jmalenko/us8ek/70-photo/PXL_20260111_123954329.jpg

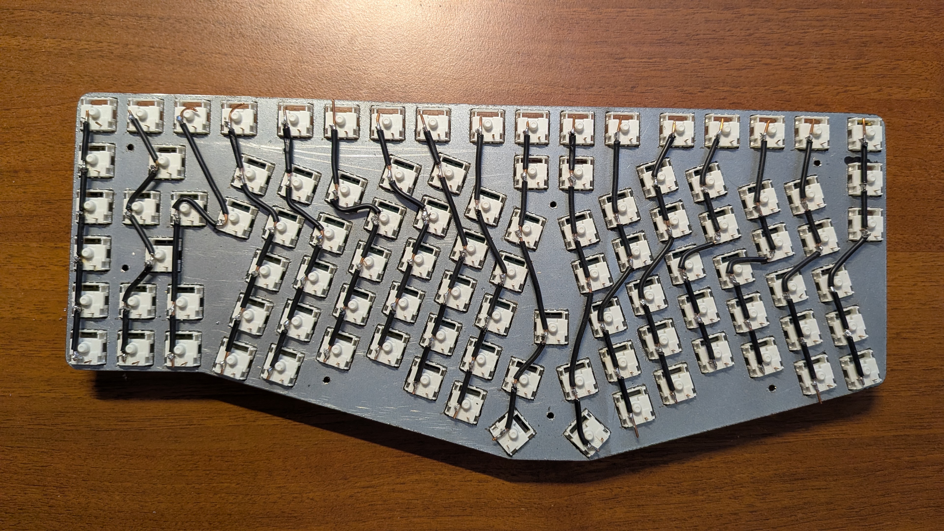
70-photo/PXL_20260111_123954329.jpg
