jmalenko/us8ek/70-photo/PXL_20260111_124021792.jpg

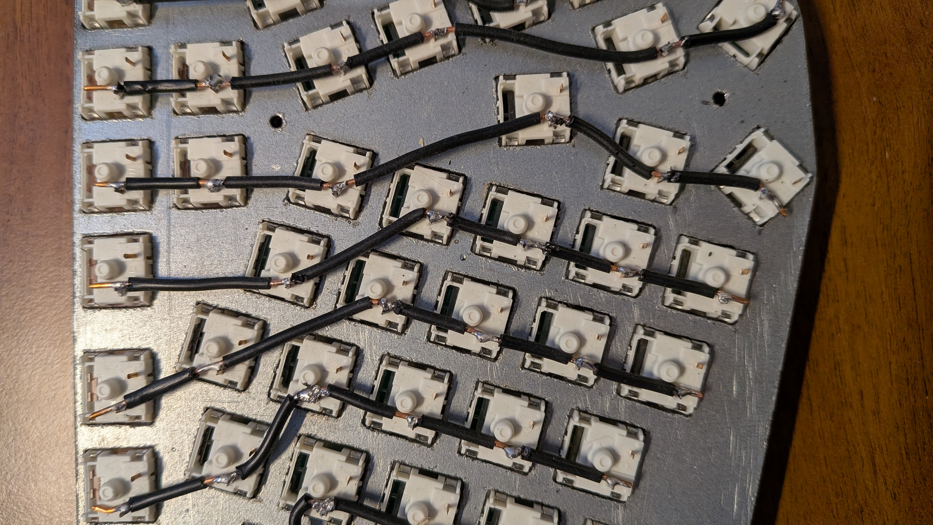
70-photo/PXL_20260111_124021792.jpg
