jmalenko/us8ek/70-photo/PXL_20260111_124031292.jpg

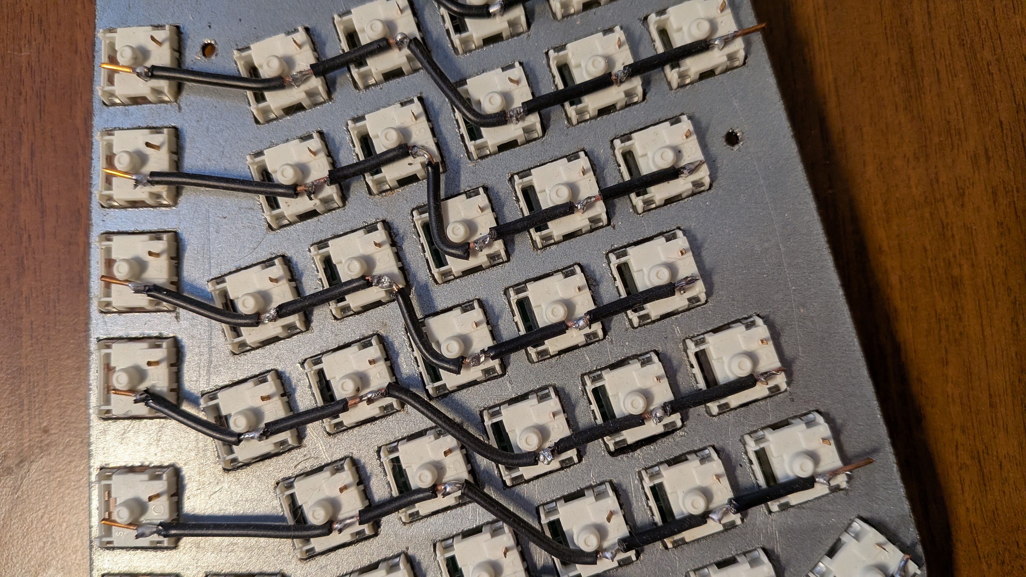
70-photo/PXL_20260111_124031292.jpg
