jmalenko/us8ek/70-photo/PXL_20260111_124134626.jpg

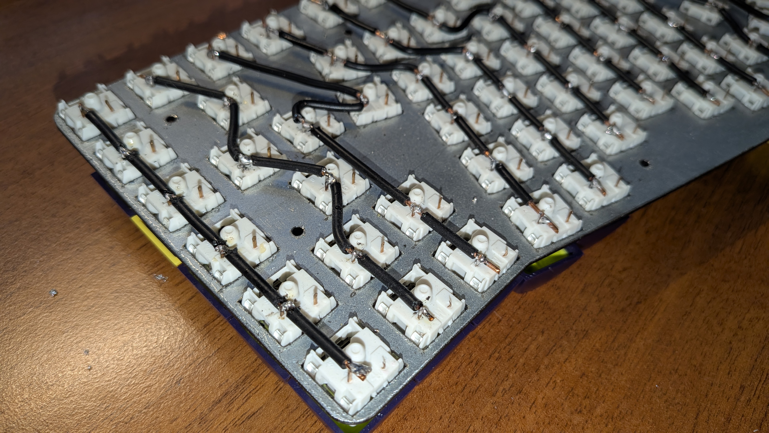
70-photo/PXL_20260111_124134626.jpg
