jmalenko/us8ek/70-photo/PXL_20260111_124154416.jpg

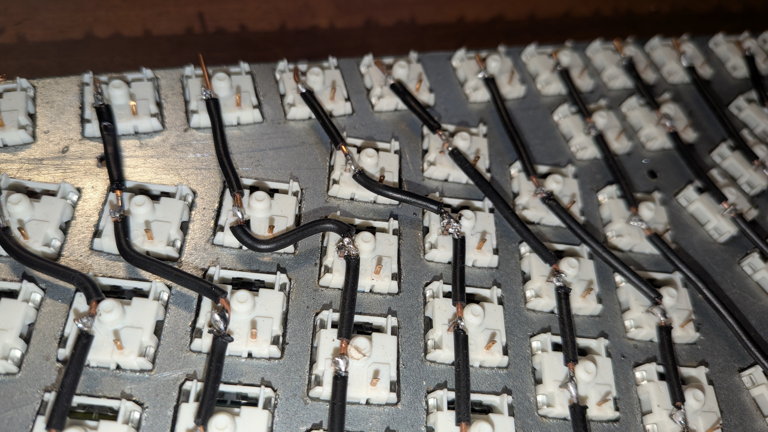
70-photo/PXL_20260111_124154416.jpg
