jmalenko/us8ek/70-photo/PXL_20260111_124345939.jpg

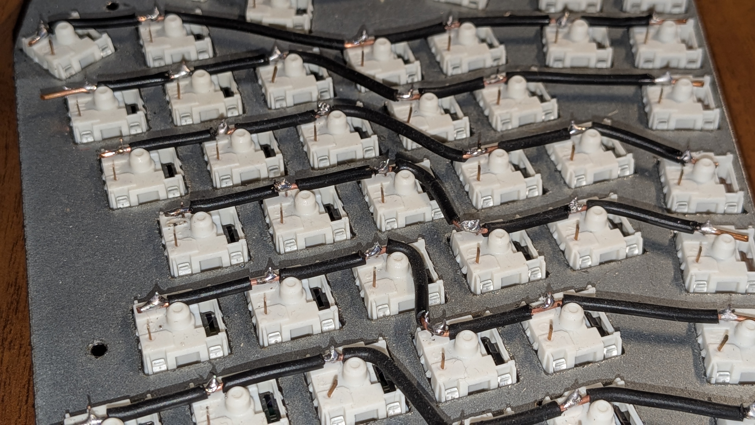
70-photo/PXL_20260111_124345939.jpg
