jmalenko/us8ek/70-photo/PXL_20260111_124404799.jpg

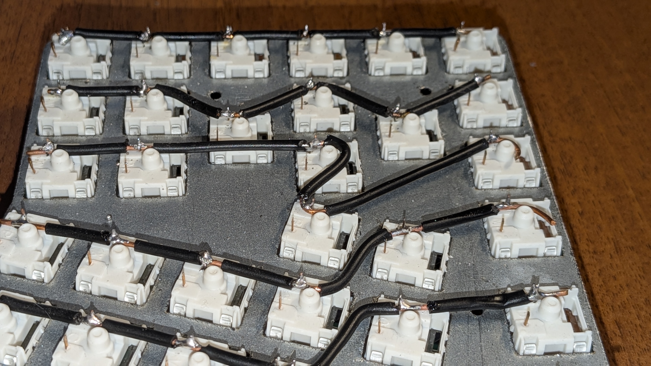
70-photo/PXL_20260111_124404799.jpg
