jmalenko/us8ek/70-photo/PXL_20260111_125549757.jpg

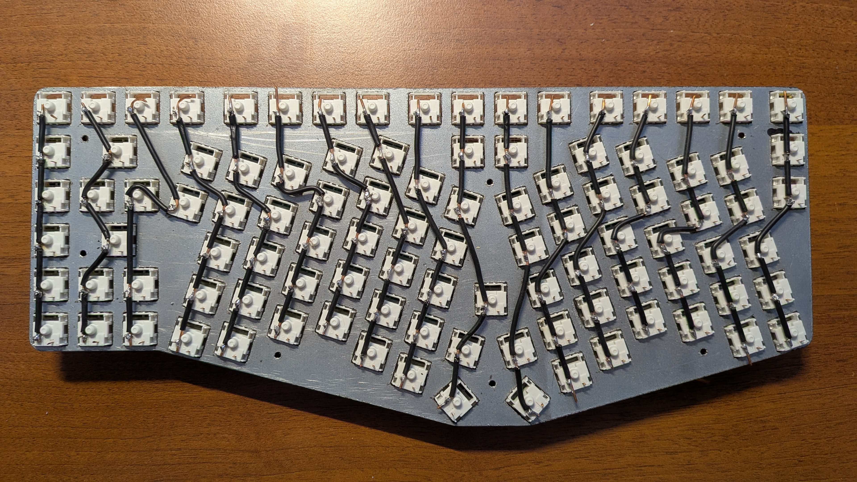
70-photo/PXL_20260111_125549757.jpg
