jmalenko/us8ek/70-photo/PXL_20260111_170305145.jpg

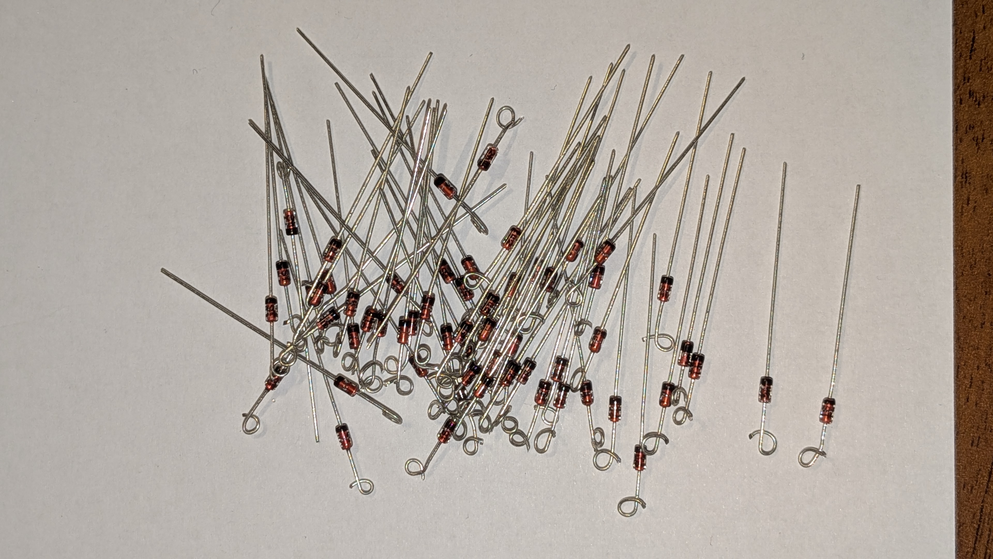
70-photo/PXL_20260111_170305145.jpg
