jmalenko/us8ek/70-photo/PXL_20260111_181909219.jpg

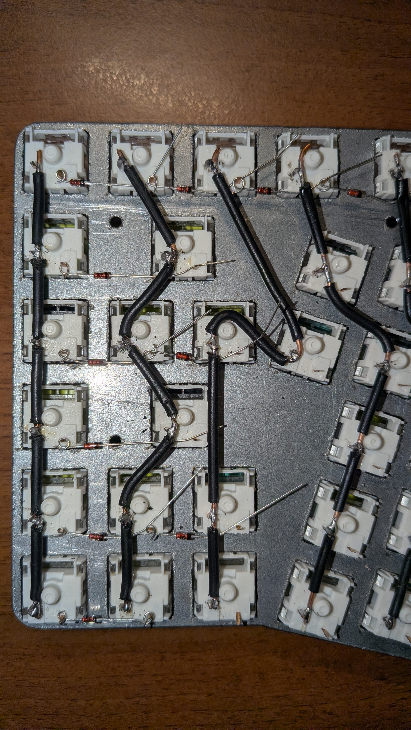
70-photo/PXL_20260111_181909219.jpg
