jmalenko/us8ek/70-photo/PXL_20260113_114841229.jpg

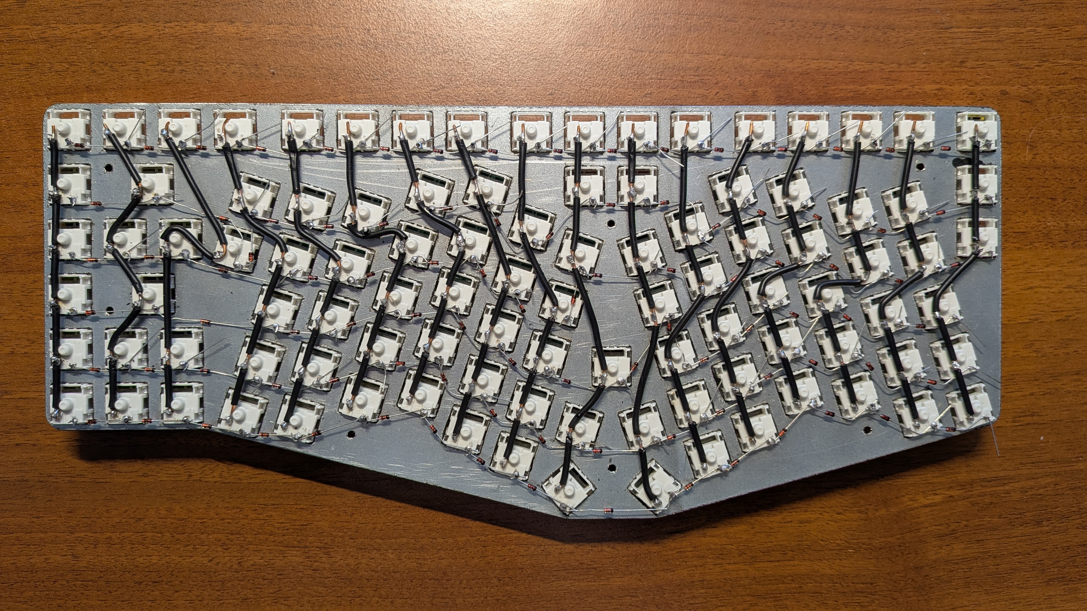
70-photo/PXL_20260113_114841229.jpg
