jmalenko/us8ek/70-photo/PXL_20260113_114855864.jpg

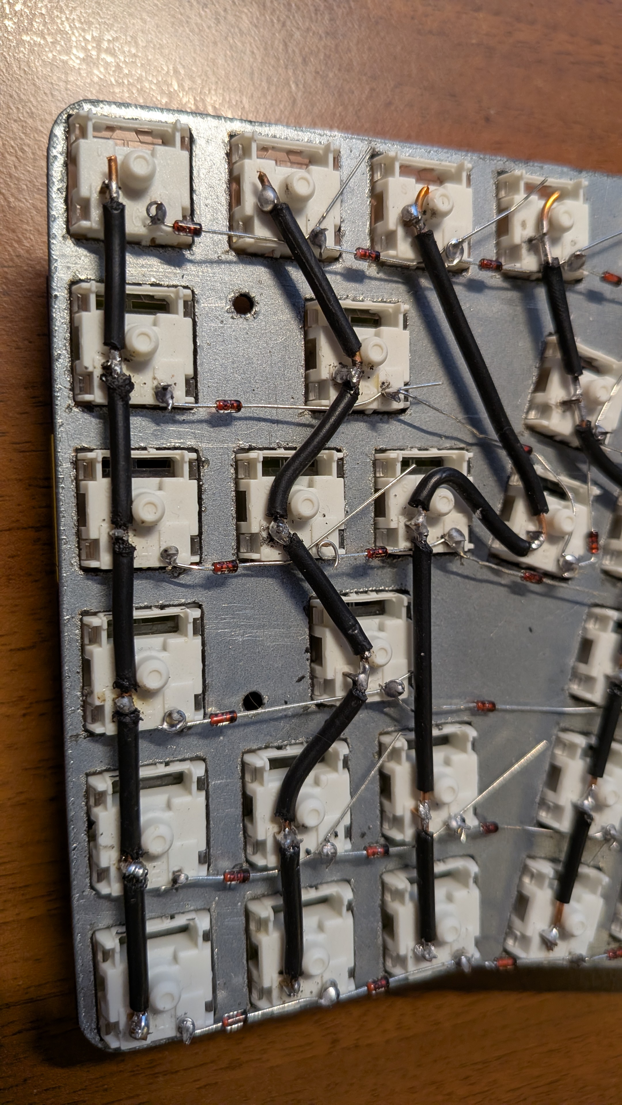
70-photo/PXL_20260113_114855864.jpg
