jmalenko/us8ek/70-photo/PXL_20260113_114857588.jpg

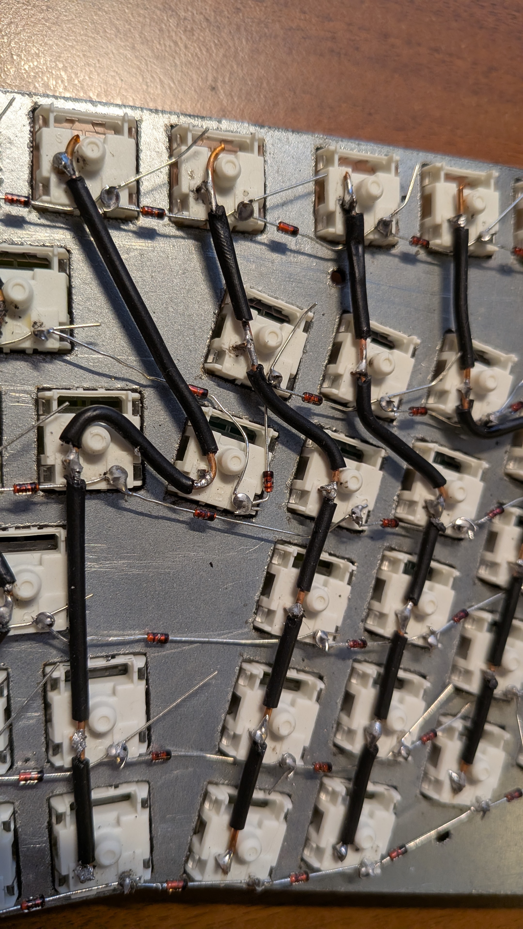
70-photo/PXL_20260113_114857588.jpg
