jmalenko/us8ek/70-photo/PXL_20260113_114900836.jpg

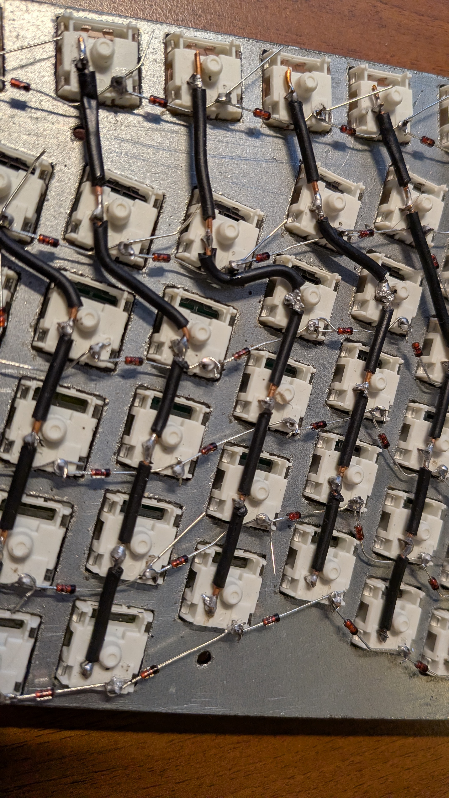
70-photo/PXL_20260113_114900836.jpg
