jmalenko/us8ek/70-photo/PXL_20260113_114911246.jpg

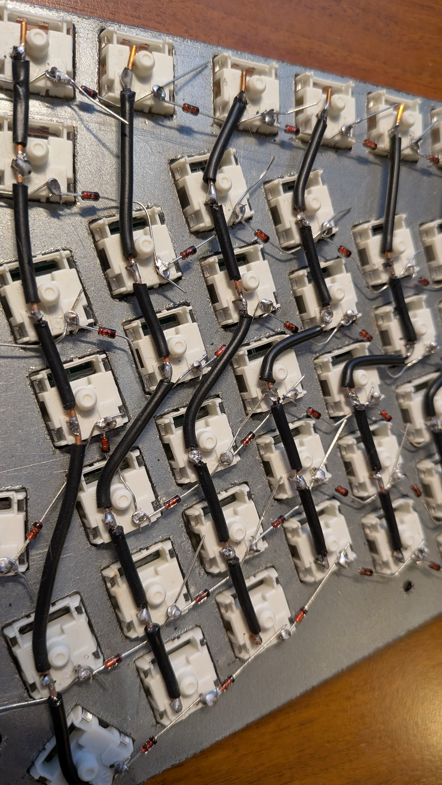
70-photo/PXL_20260113_114911246.jpg
