jmalenko/us8ek/70-photo/PXL_20260113_114915414.MACRO_FOCUS.jpg

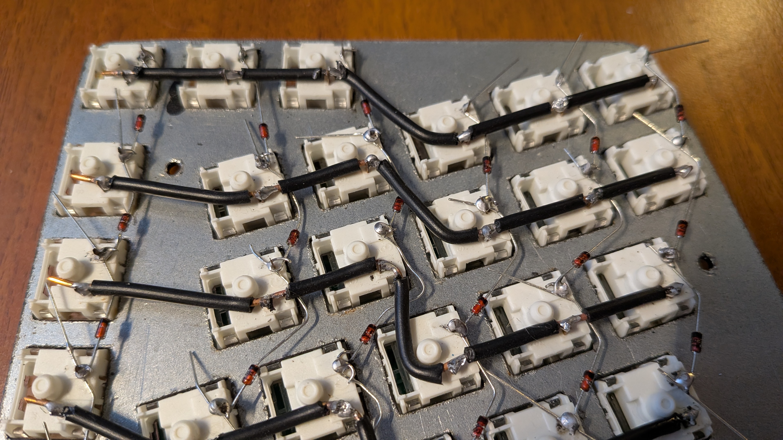
70-photo/PXL_20260113_114915414.MACRO_FOCUS.jpg
