jmalenko/us8ek/70-photo/PXL_20260113_120844157.jpg

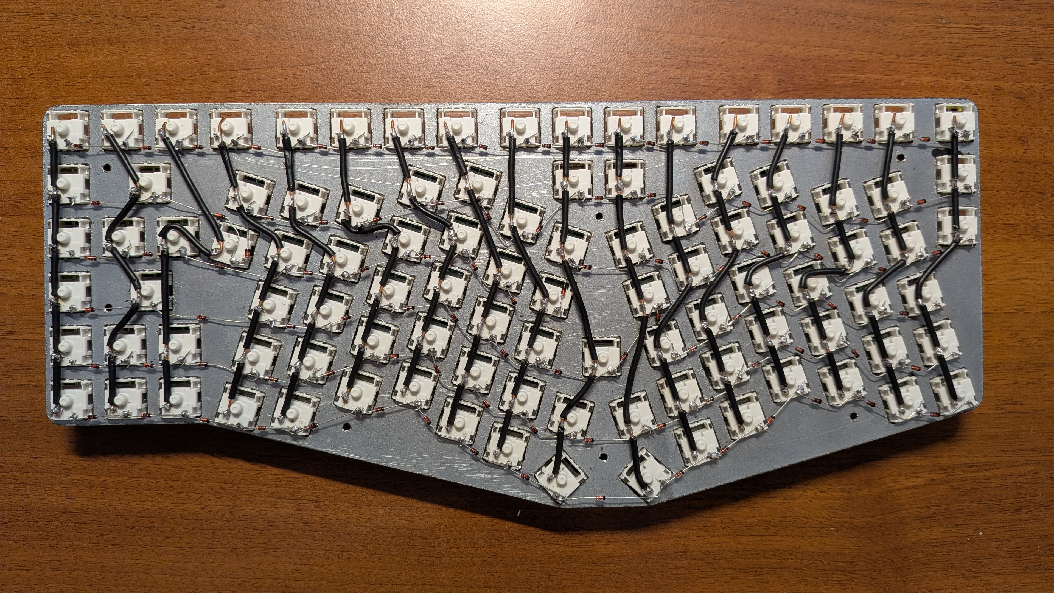
70-photo/PXL_20260113_120844157.jpg
