jmalenko/us8ek/70-photo/PXL_20260113_120919098.jpg

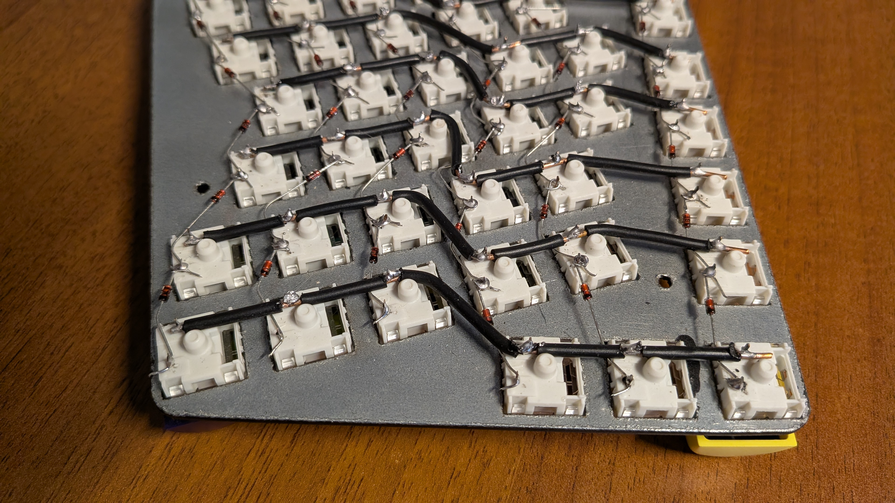
70-photo/PXL_20260113_120919098.jpg
