jmalenko/us8ek/70-photo/PXL_20260113_120921176.jpg

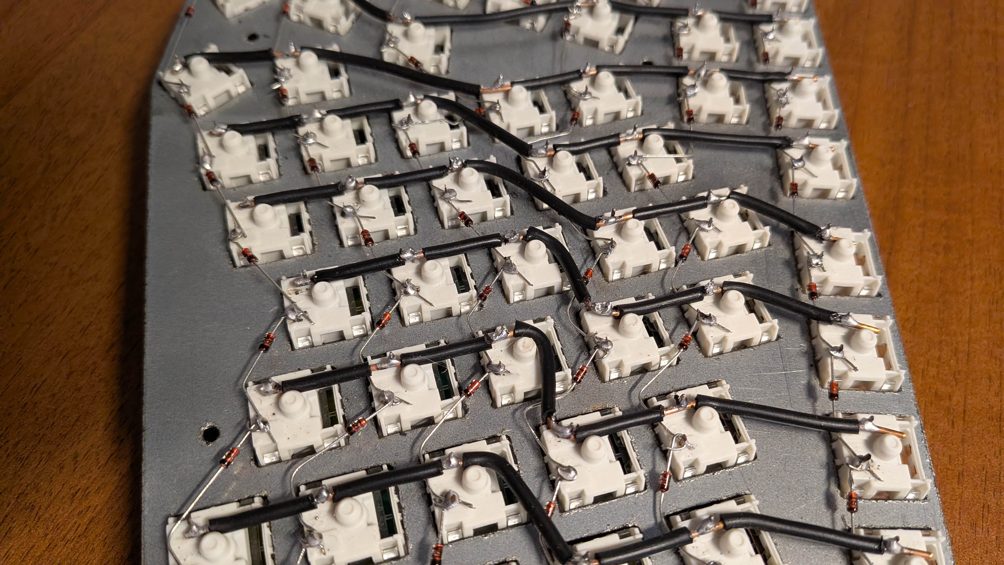
70-photo/PXL_20260113_120921176.jpg
