jmalenko/us8ek/70-photo/PXL_20260113_120925056.jpg

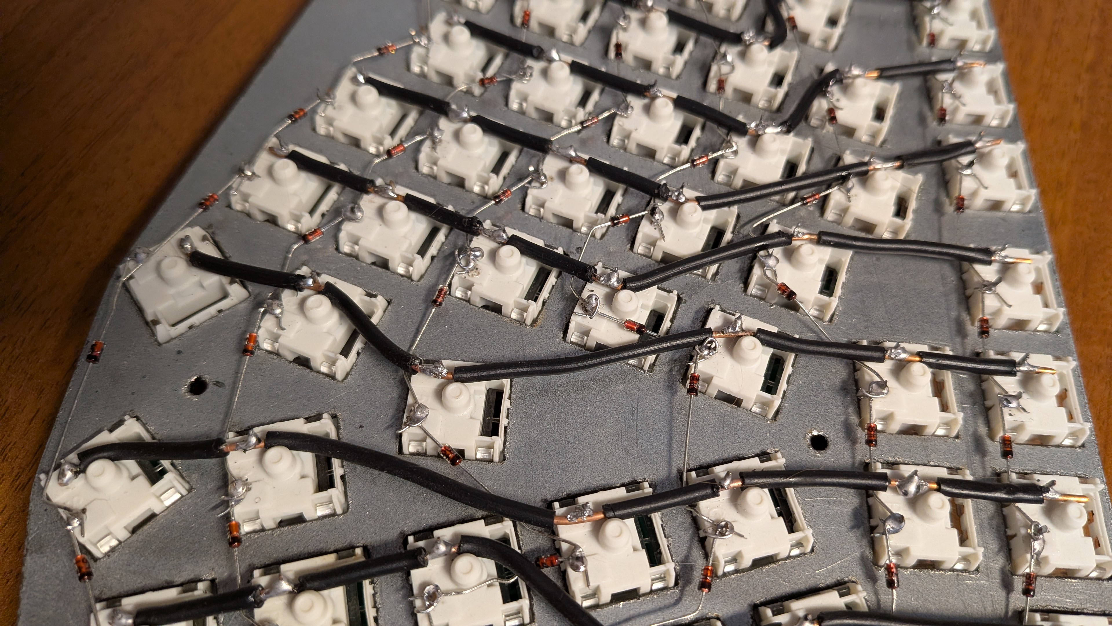
70-photo/PXL_20260113_120925056.jpg
