jmalenko/us8ek/70-photo/PXL_20260113_120930169.jpg

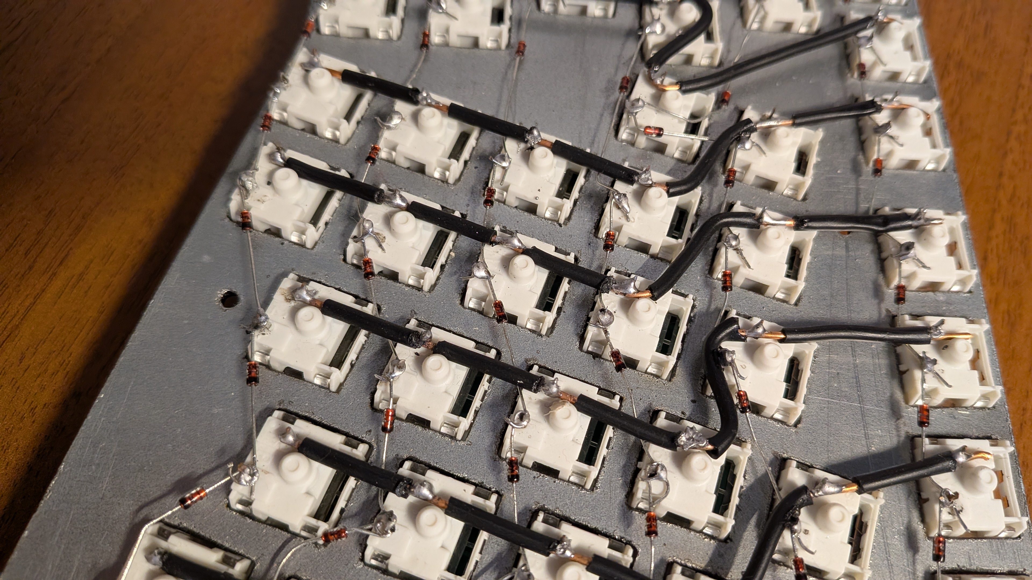
70-photo/PXL_20260113_120930169.jpg
