jmalenko/us8ek/70-photo/PXL_20260113_120933175.jpg

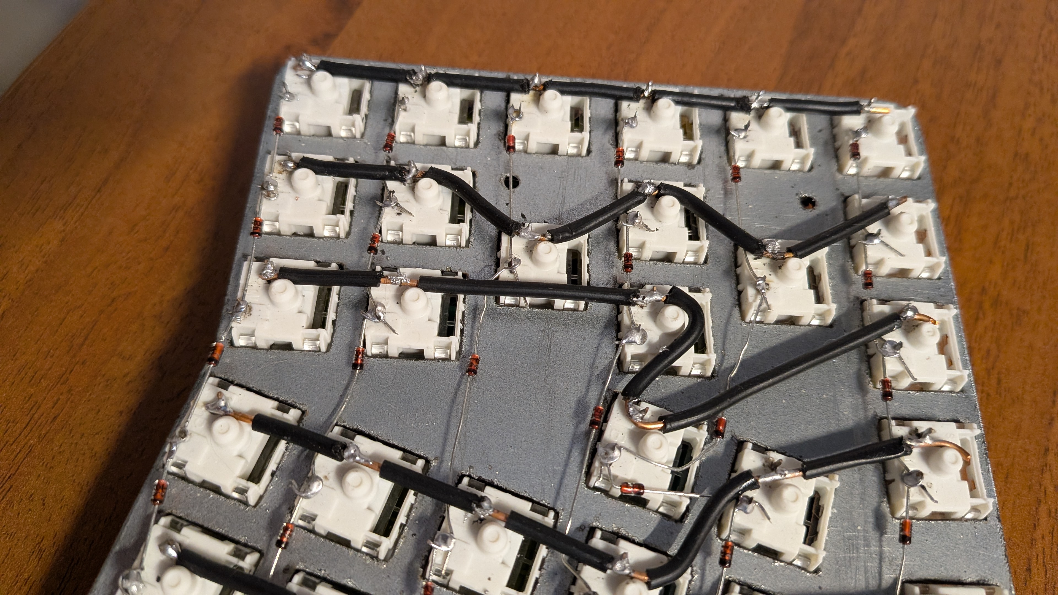
70-photo/PXL_20260113_120933175.jpg
