jmalenko/us8ek/70-photo/PXL_20260113_120949158.jpg

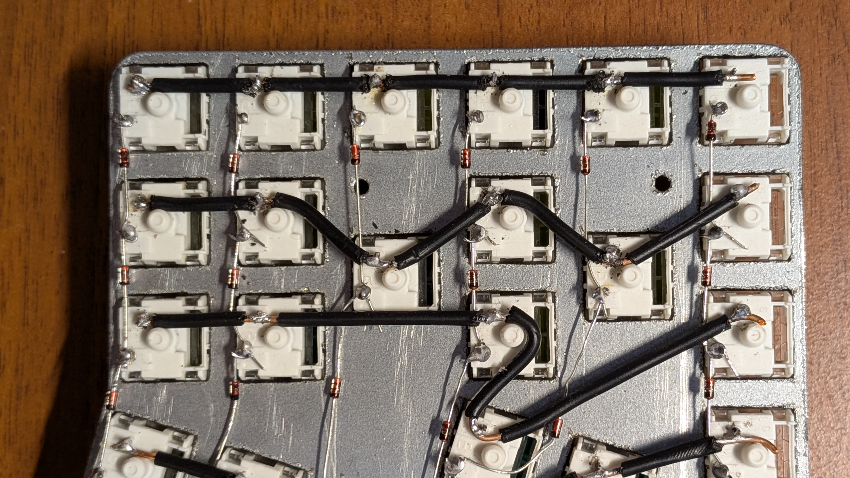
70-photo/PXL_20260113_120949158.jpg
