jmalenko/us8ek/70-photo/PXL_20260113_120952211.jpg

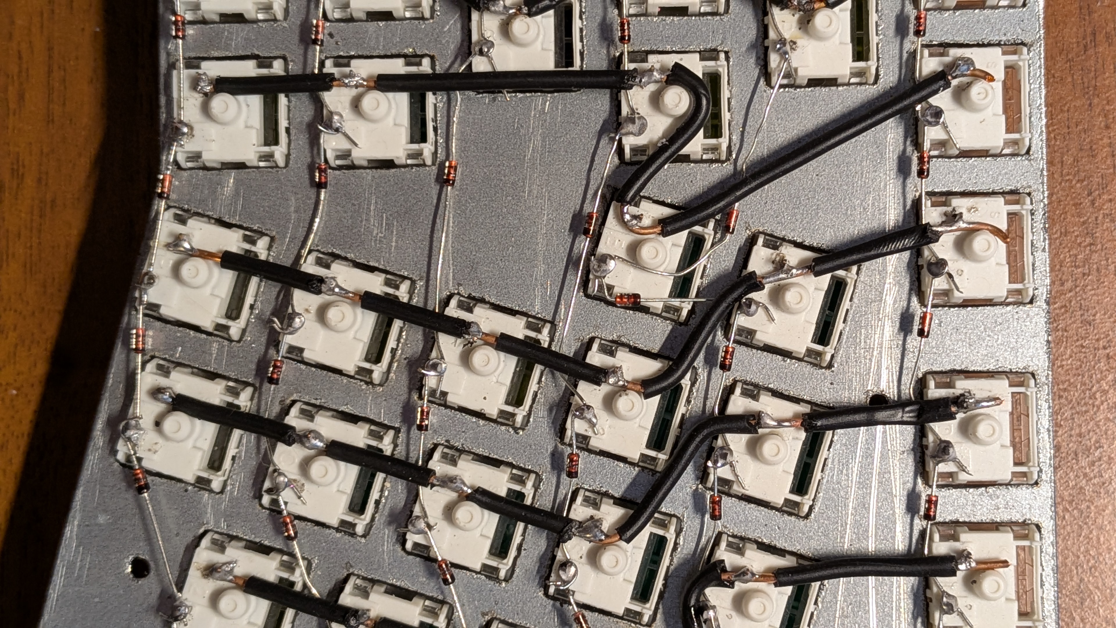
70-photo/PXL_20260113_120952211.jpg
