jmalenko/us8ek/70-photo/PXL_20260113_120954827.jpg

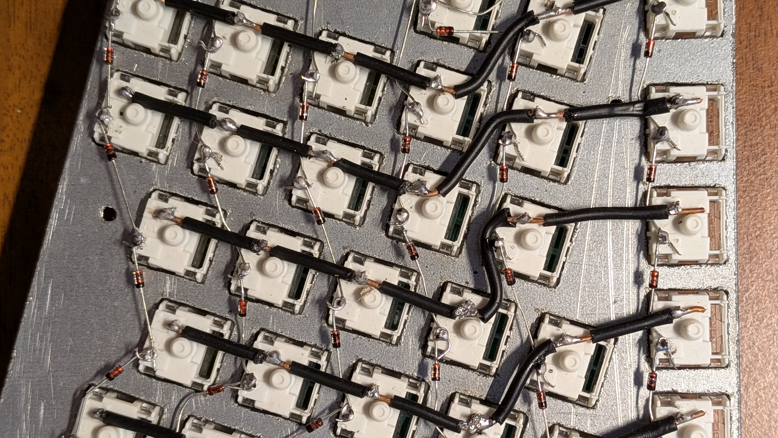
70-photo/PXL_20260113_120954827.jpg
