jmalenko/us8ek/70-photo/PXL_20260113_120957864.jpg

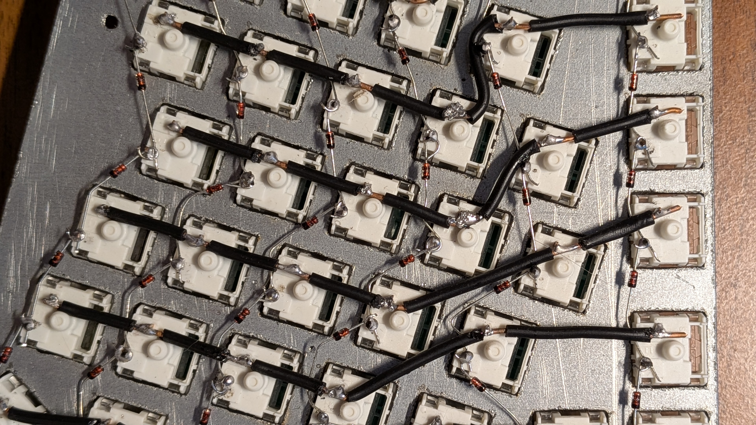
70-photo/PXL_20260113_120957864.jpg
