jmalenko/us8ek/70-photo/PXL_20260113_121008801.jpg

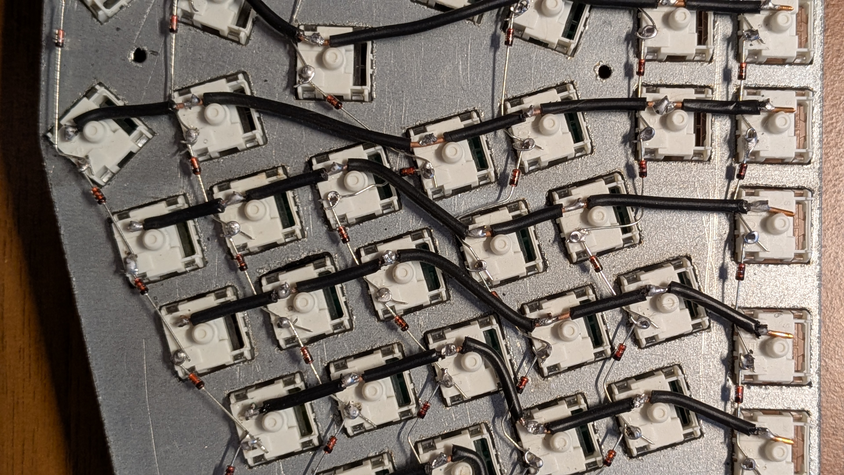
70-photo/PXL_20260113_121008801.jpg
