jmalenko/us8ek/70-photo/PXL_20260113_121011084.jpg

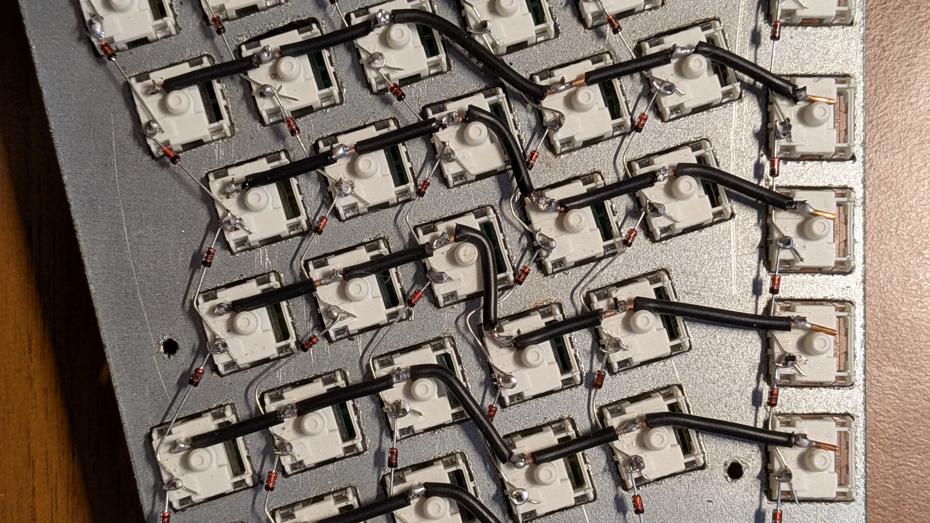
70-photo/PXL_20260113_121011084.jpg
