jmalenko/us8ek/70-photo/PXL_20260113_160840646.jpg

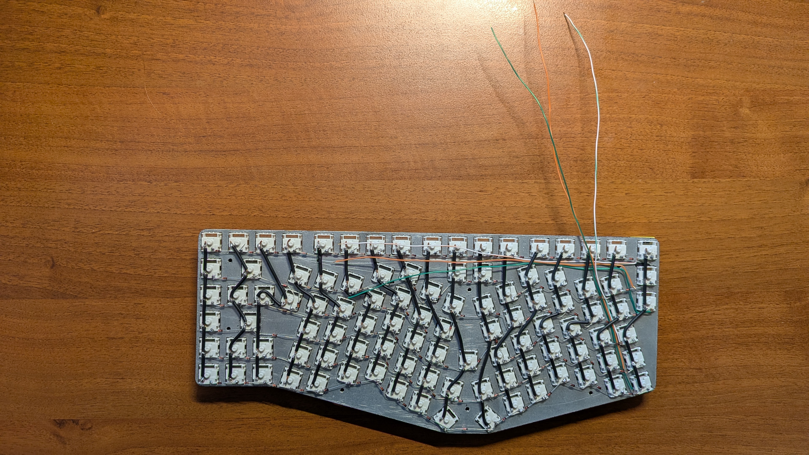
70-photo/PXL_20260113_160840646.jpg
