jmalenko/us8ek/70-photo/PXL_20260113_171134061.jpg

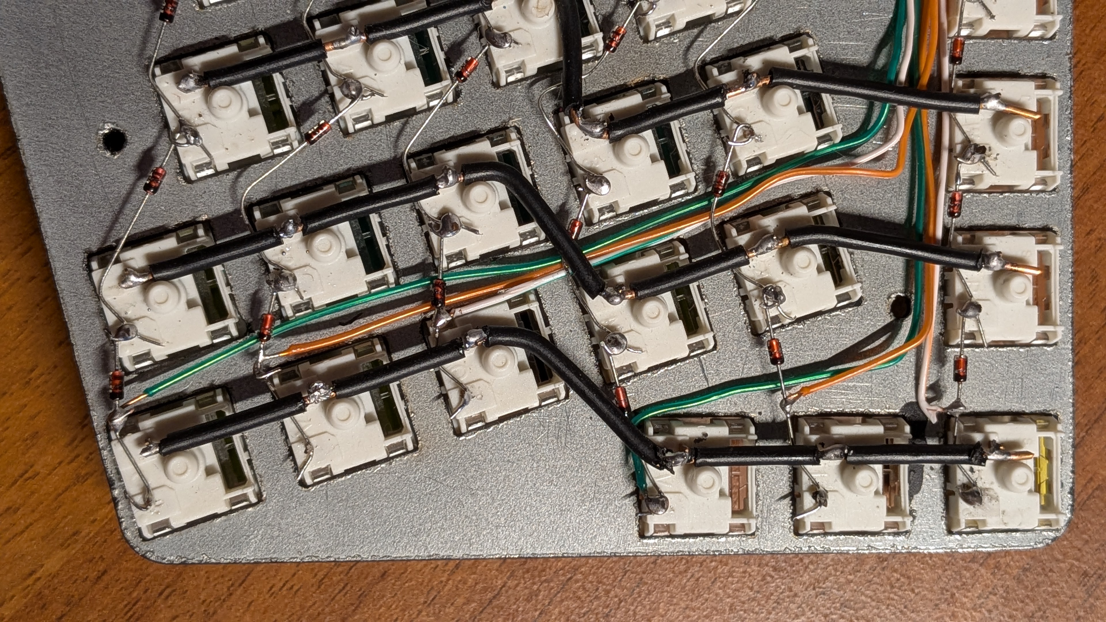
70-photo/PXL_20260113_171134061.jpg
