jmalenko/us8ek/70-photo/PXL_20260113_171150978.jpg

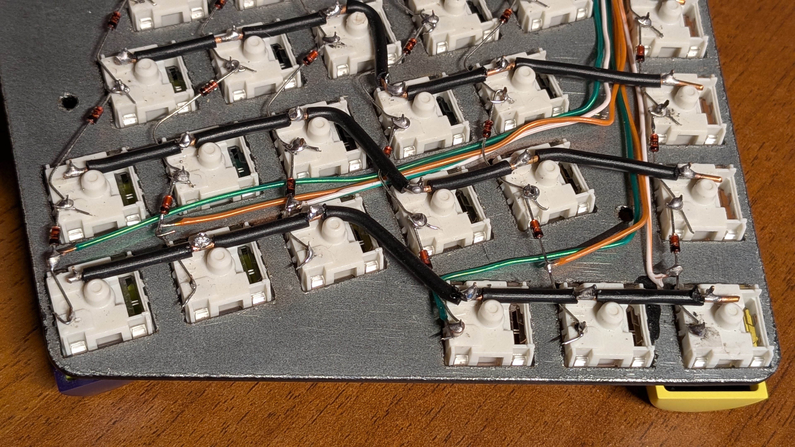
70-photo/PXL_20260113_171150978.jpg
