jmalenko/us8ek/70-photo/PXL_20260113_171700001.jpg

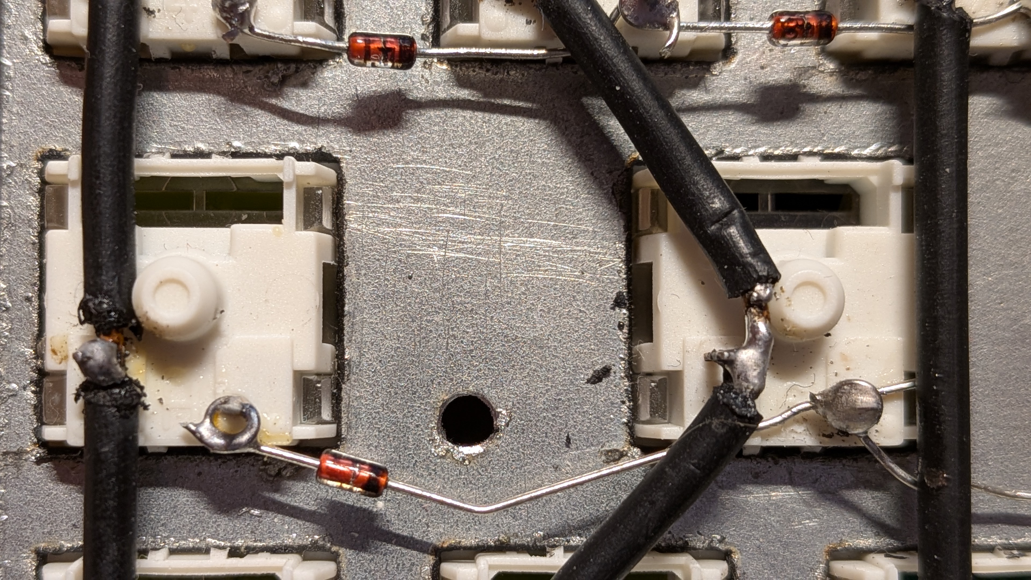
70-photo/PXL_20260113_171700001.jpg
