jmalenko/us8ek/70-photo/PXL_20260116_120629643.jpg

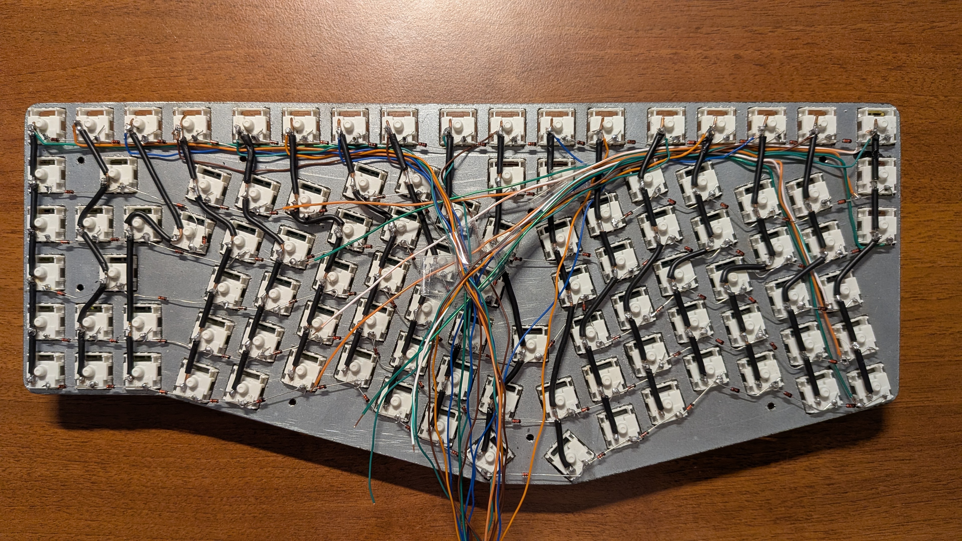
70-photo/PXL_20260116_120629643.jpg
