jmalenko/us8ek/70-photo/PXL_20260116_120638237.jpg

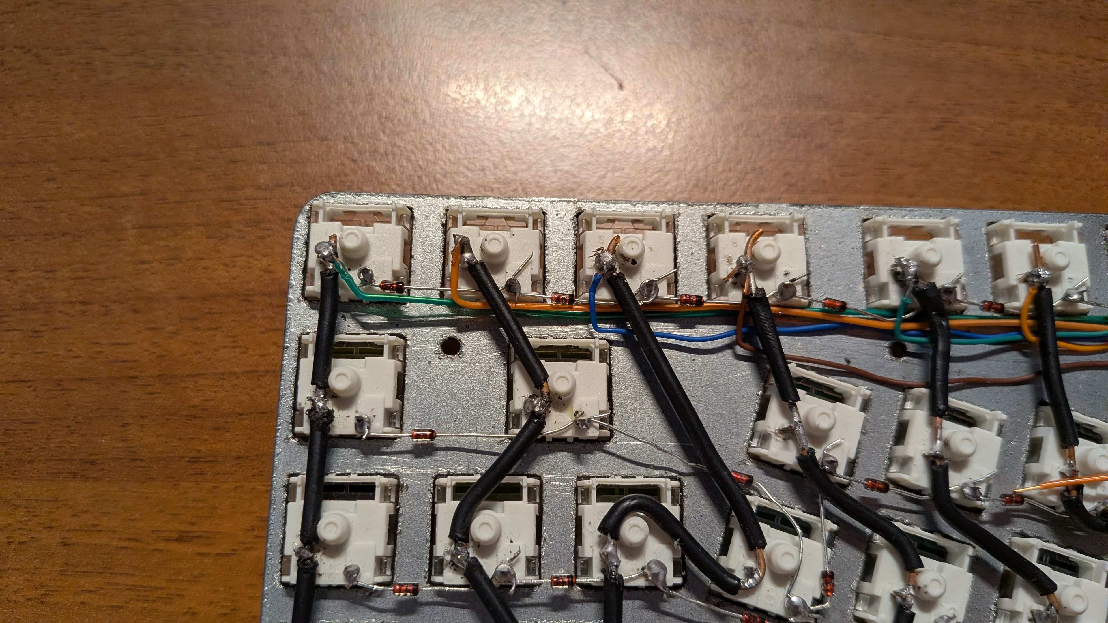
70-photo/PXL_20260116_120638237.jpg
