jmalenko/us8ek/70-photo/PXL_20260116_120748354.jpg

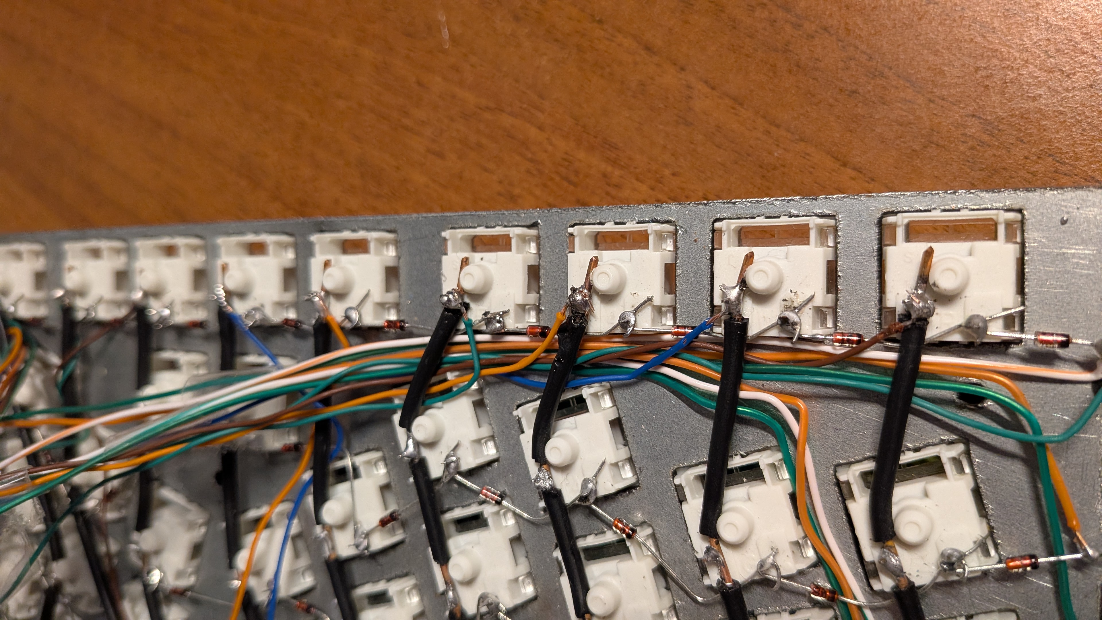
70-photo/PXL_20260116_120748354.jpg
