jmalenko/us8ek/70-photo/PXL_20260116_120753417.jpg

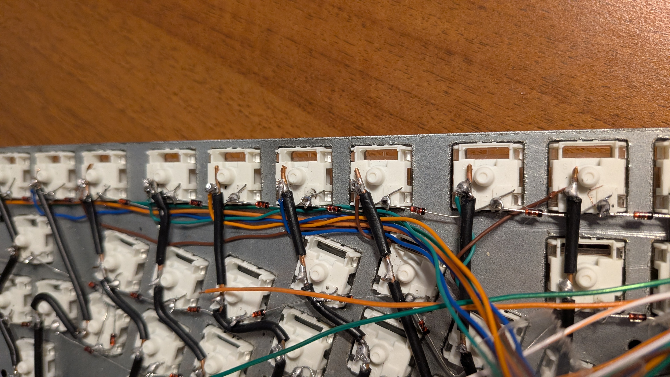
70-photo/PXL_20260116_120753417.jpg
