jmalenko/us8ek/70-photo/PXL_20260116_120758351.jpg

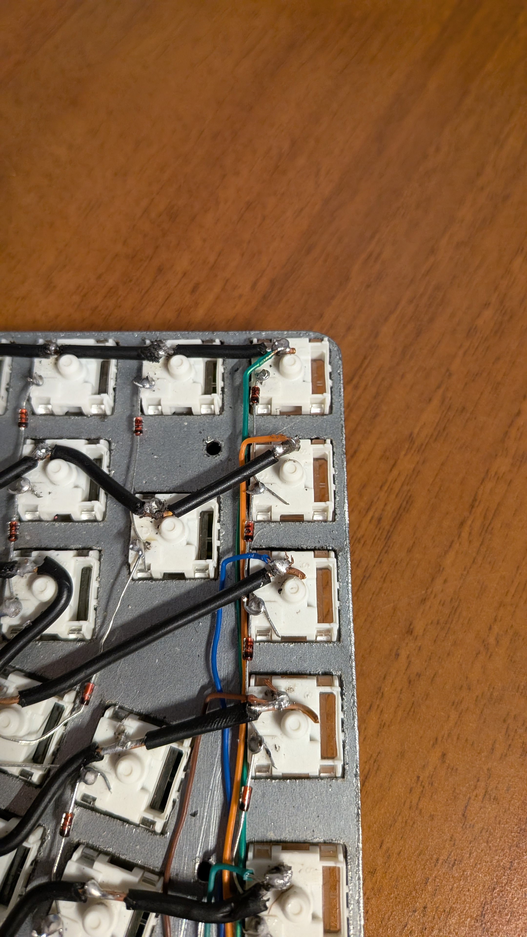
70-photo/PXL_20260116_120758351.jpg
