jmalenko/us8ek/70-photo/PXL_20260117_180453187-Find what's wrong.jpg

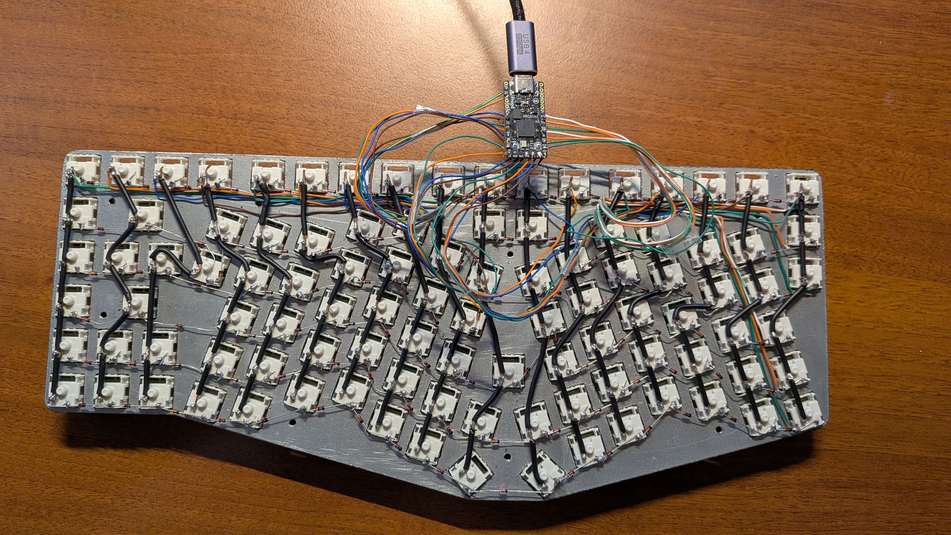
70-photo/PXL_20260117_180453187-Find what's wrong.jpg
