jmalenko/us8ek/70-photo/PXL_20260117_180509974.jpg

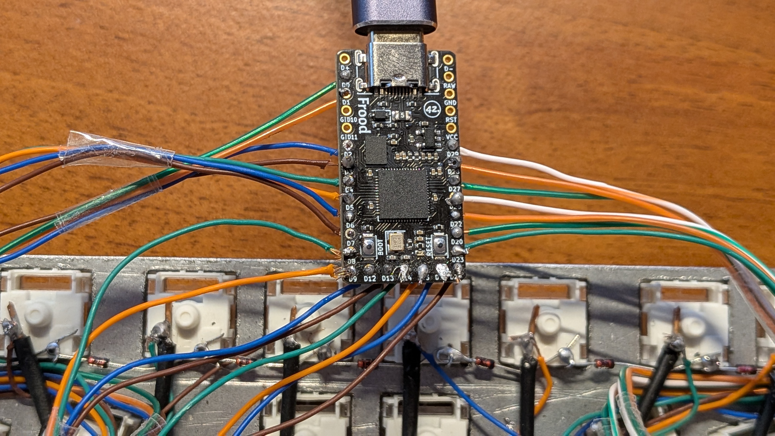
70-photo/PXL_20260117_180509974.jpg
