jmalenko/us8ek/70-photo/PXL_20260205_193144027.jpg

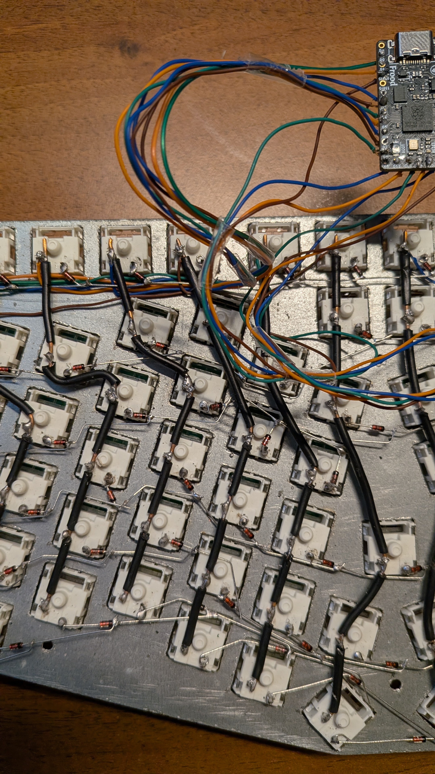
70-photo/PXL_20260205_193144027.jpg
