jmalenko/us8ek/70-photo/PXL_20260205_193145945.jpg

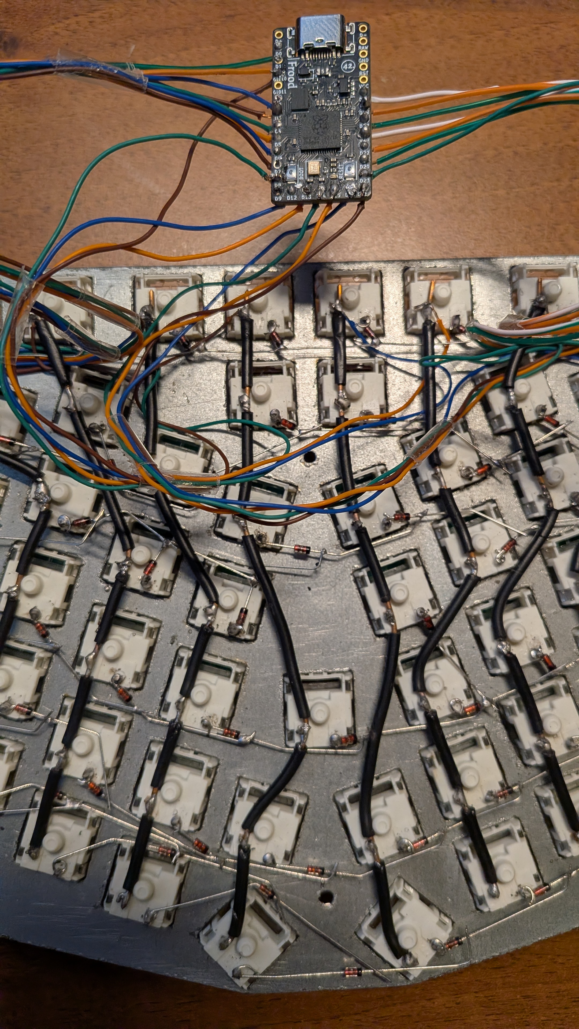
70-photo/PXL_20260205_193145945.jpg
