jmalenko/us8ek/70-photo/PXL_20260205_193208209.jpg

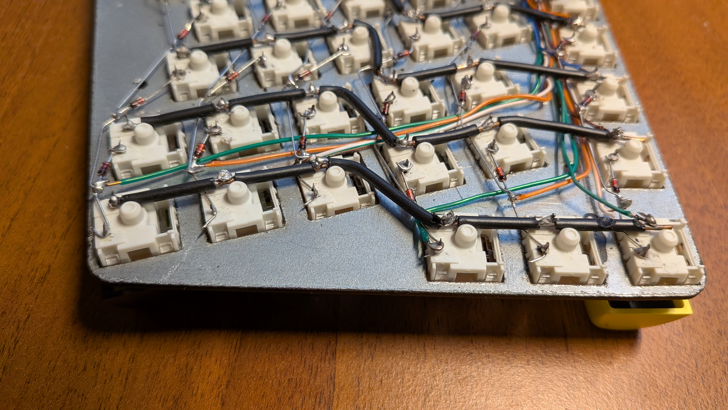
70-photo/PXL_20260205_193208209.jpg
