jmalenko/us8ek/70-photo/PXL_20260205_193209658.jpg

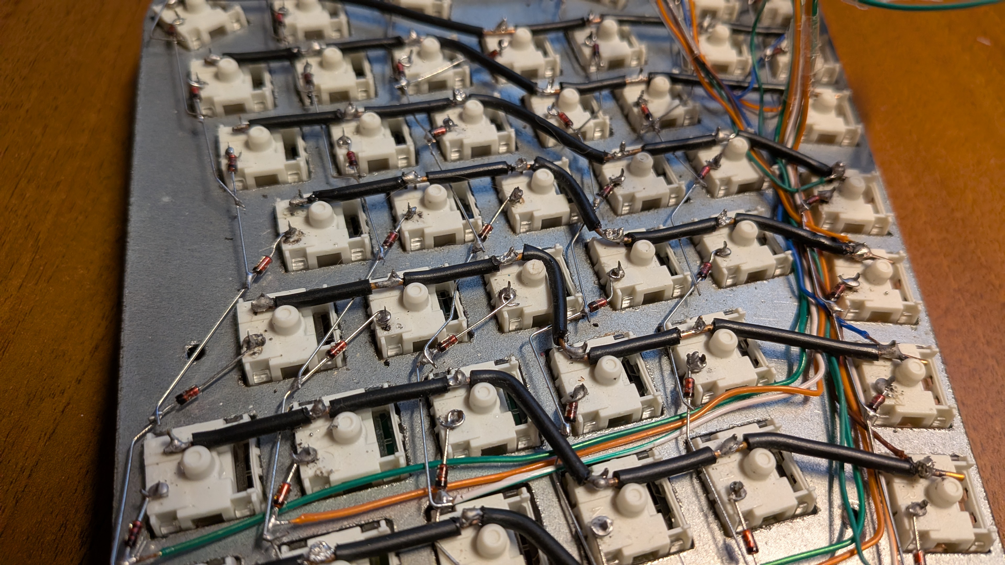
70-photo/PXL_20260205_193209658.jpg
