jmalenko/us8ek/70-photo/PXL_20260205_193210949.jpg

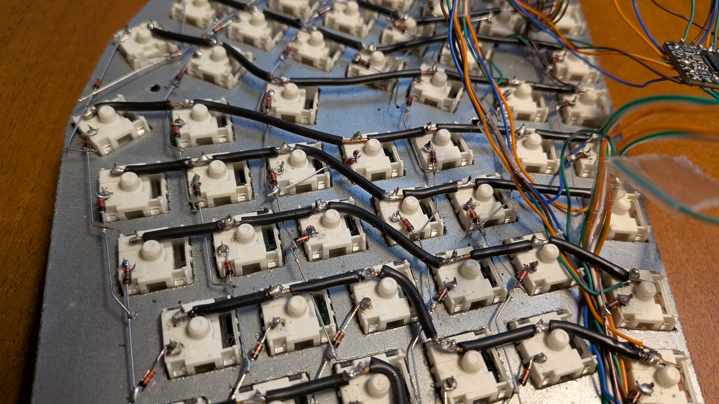
70-photo/PXL_20260205_193210949.jpg
