jmalenko/us8ek/70-photo/PXL_20260205_193213651.jpg

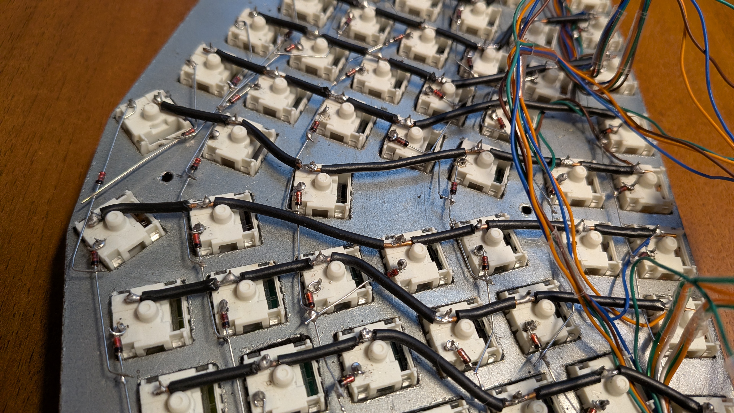
70-photo/PXL_20260205_193213651.jpg
