jmalenko/us8ek/70-photo/PXL_20260205_193218937.jpg

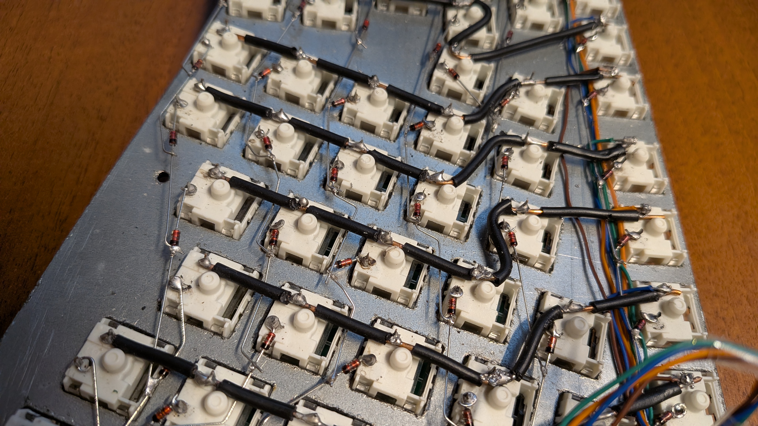
70-photo/PXL_20260205_193218937.jpg
