jmalenko/us8ek/70-photo/PXL_20260205_193313311.jpg

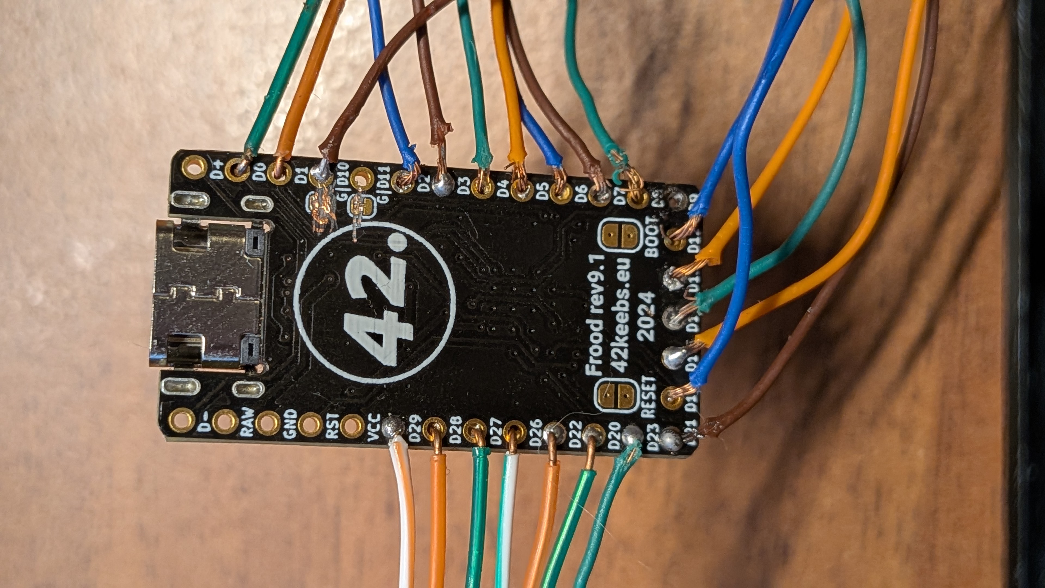
70-photo/PXL_20260205_193313311.jpg
