jmalenko/us8ek/70-photo/PXL_20260205_193432638.jpg

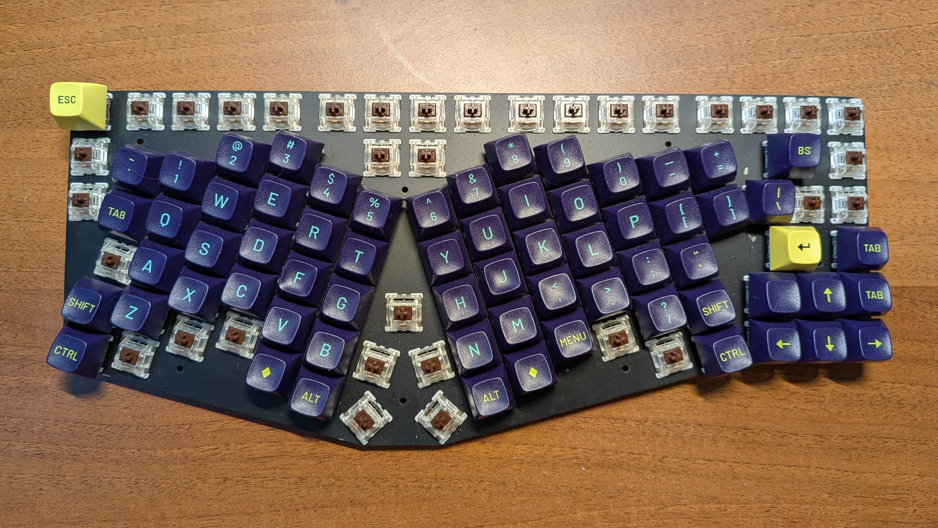
70-photo/PXL_20260205_193432638.jpg
