jmalenko/us8ek/70-photo/PXL_20260206_181301824.jpg

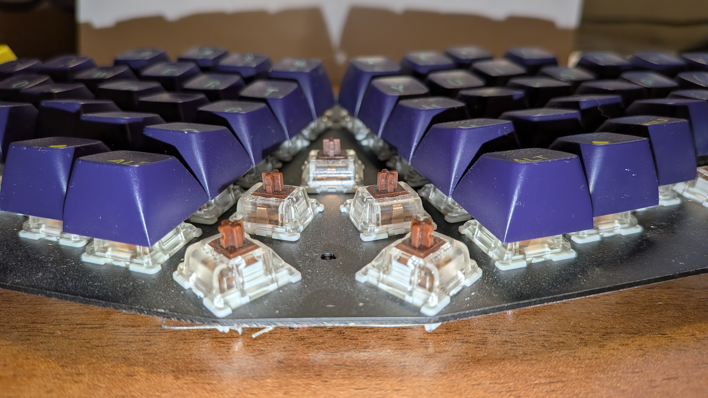
70-photo/PXL_20260206_181301824.jpg
