jmalenko/us8ek/70-photo/PXL_20260206_181404621.jpg

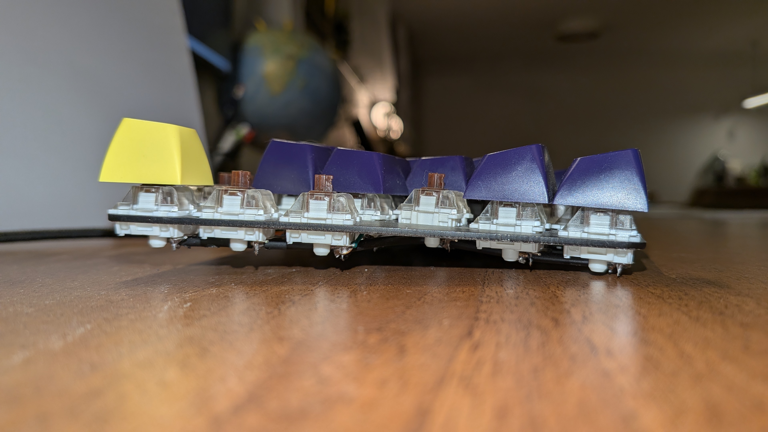
70-photo/PXL_20260206_181404621.jpg
