jmalenko/us8ek/70-photo/PXL_20260306_195609725.jpg

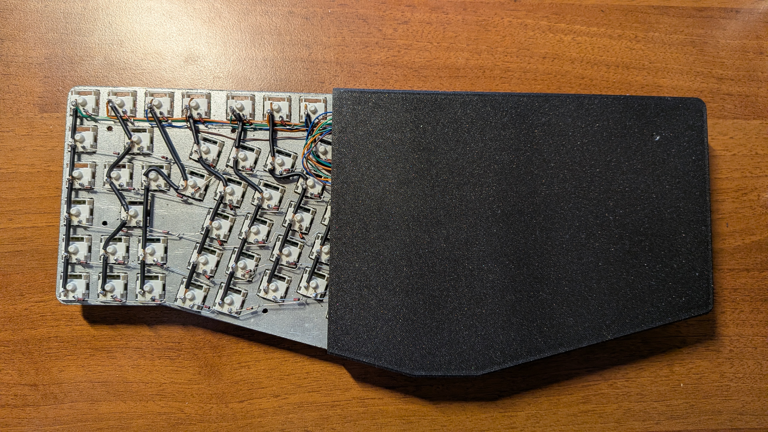
70-photo/PXL_20260306_195609725.jpg
