jmalenko/us8ek/70-photo/PXL_20260309_160319873-with case.jpg

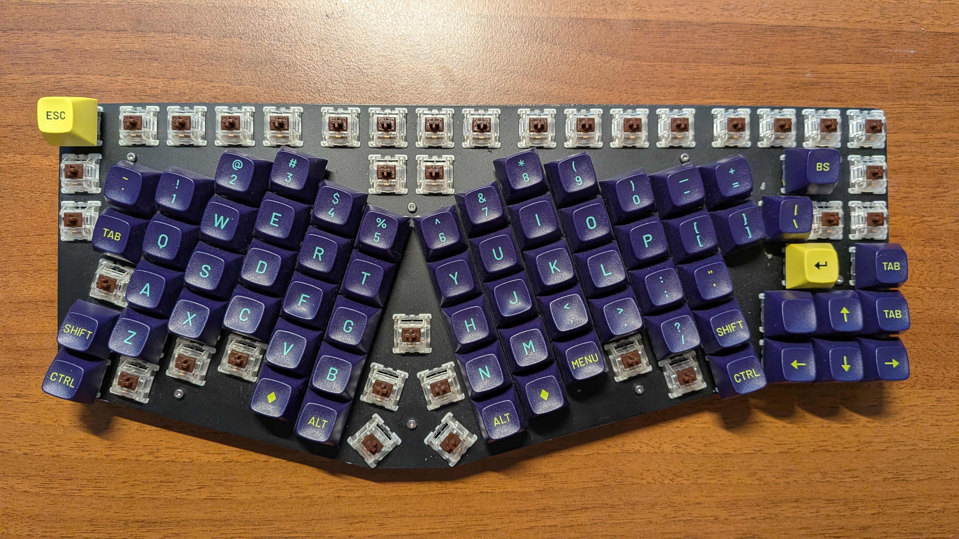
70-photo/PXL_20260309_160319873-with case.jpg
