jmalenko/us8ek/70-photo/PXL_20260309_160423577.jpg

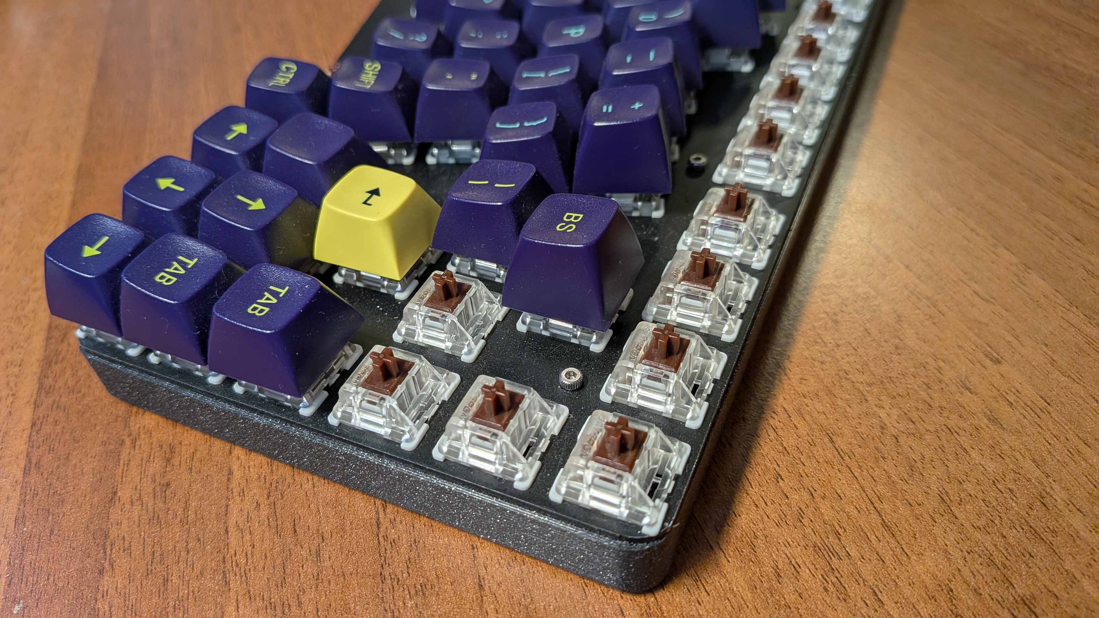
70-photo/PXL_20260309_160423577.jpg
