jmalenko/us8ek/70-photo/PXL_20260309_160443895.jpg

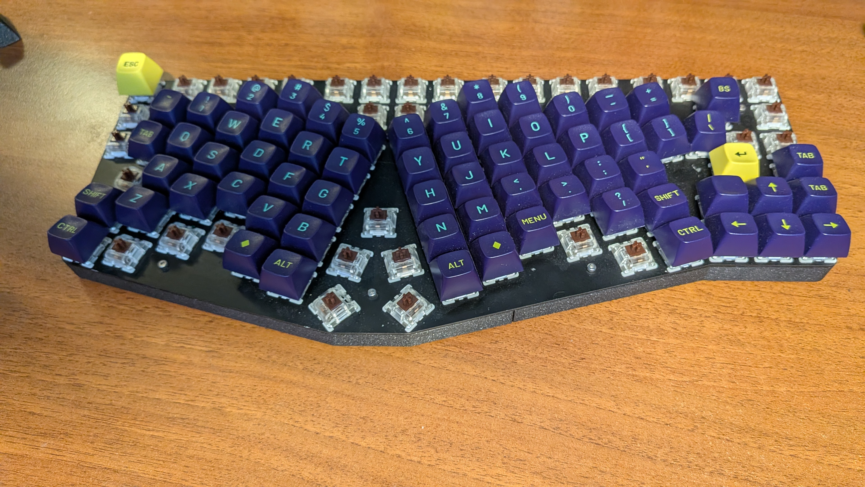
70-photo/PXL_20260309_160443895.jpg
