jmalenko/us8ek/70-photo/PXL_20260318_181733790.jpg

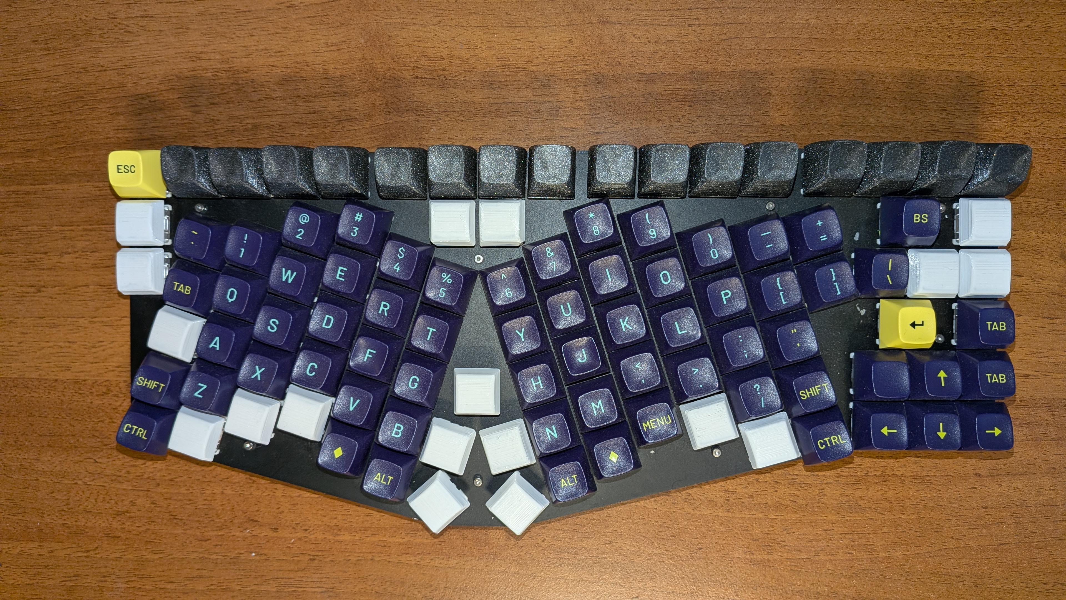
70-photo/PXL_20260318_181733790.jpg
