jmalenko/us8ek/70-photo/PXL_20260318_181847163..jpg

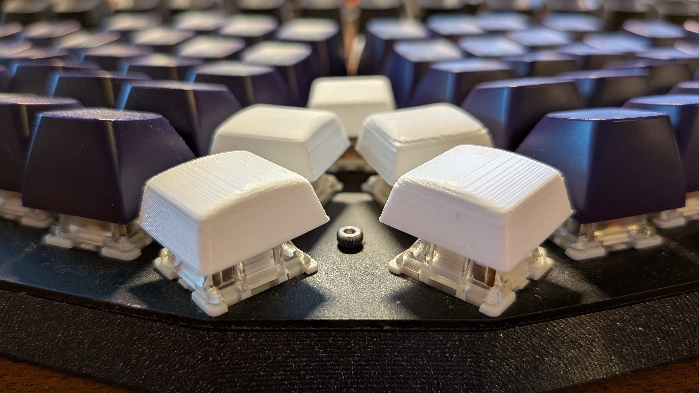
70-photo/PXL_20260318_181847163..jpg
