jmalenko/us8ek/90-research/inspiration/4 rows-7etnh4hrjyrd1.jpg

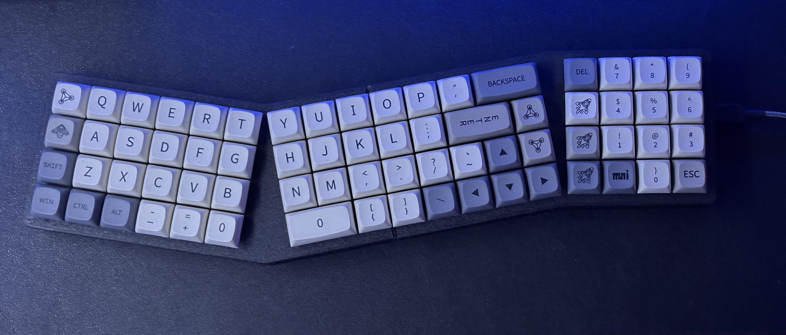
90-research/inspiration/4 rows-7etnh4hrjyrd1.jpg
