jmalenko/us8ek/11-wiring/wiring-plan-flipped-for-actual-wiring.png

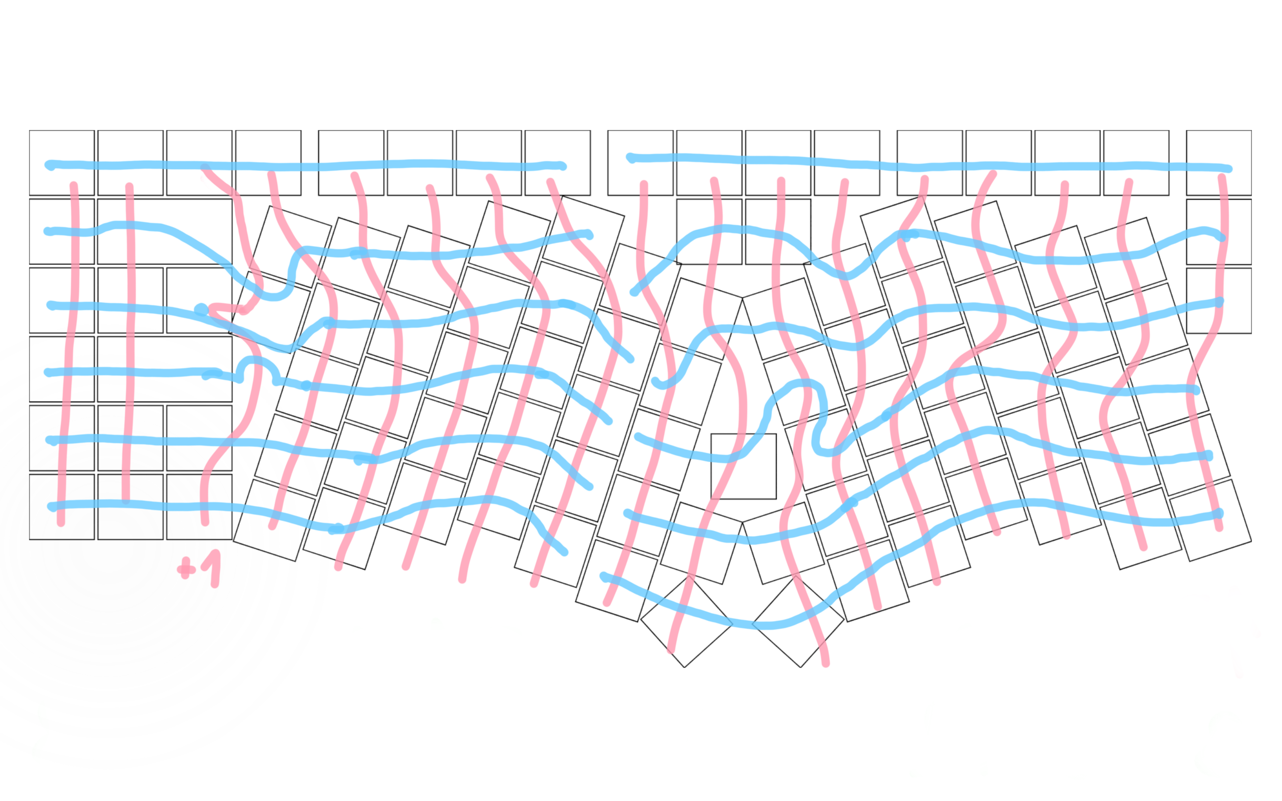
11-wiring/wiring-plan-flipped-for-actual-wiring.png
